SineScire/LilyCase/Files/GasketHard.stl

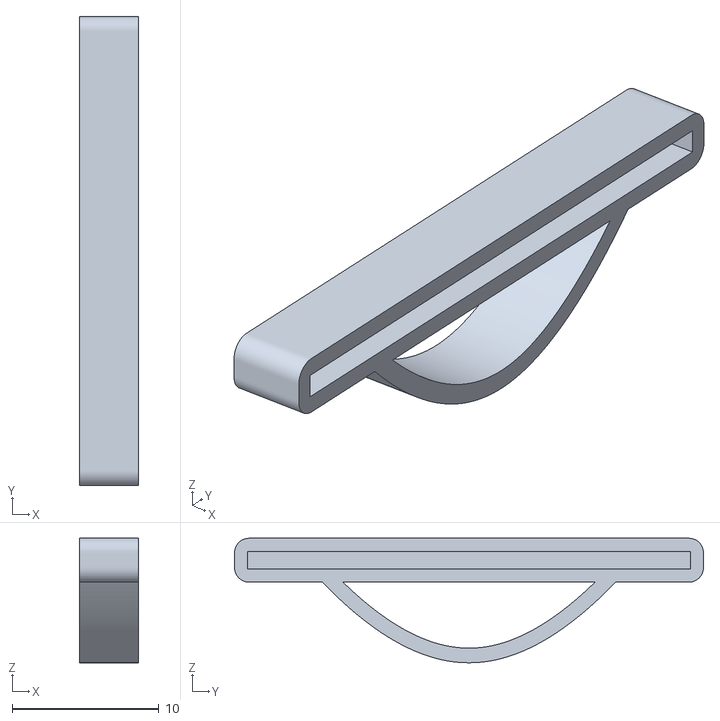
[picture p12: CAD file, 2025-05-26]
Files/GasketHard.stl
4.00 x 32.0 x 8.50
