SineScire/LilyCase/Files/GasketMedium.stl

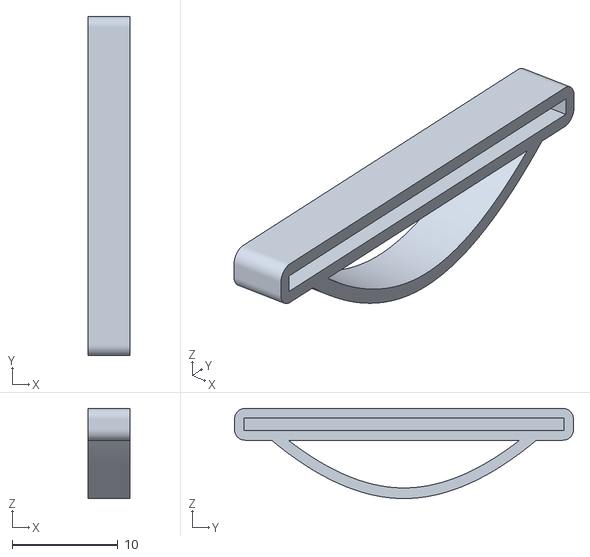
[picture p13: CAD file, 2025-05-26]
Files/GasketMedium.stl
4.00 x 32.0 x 8.50
